funvill/mixxtape/artwork/mixxtape-b-side-peony-flower-centres-template-100-33mm-300dpi.png

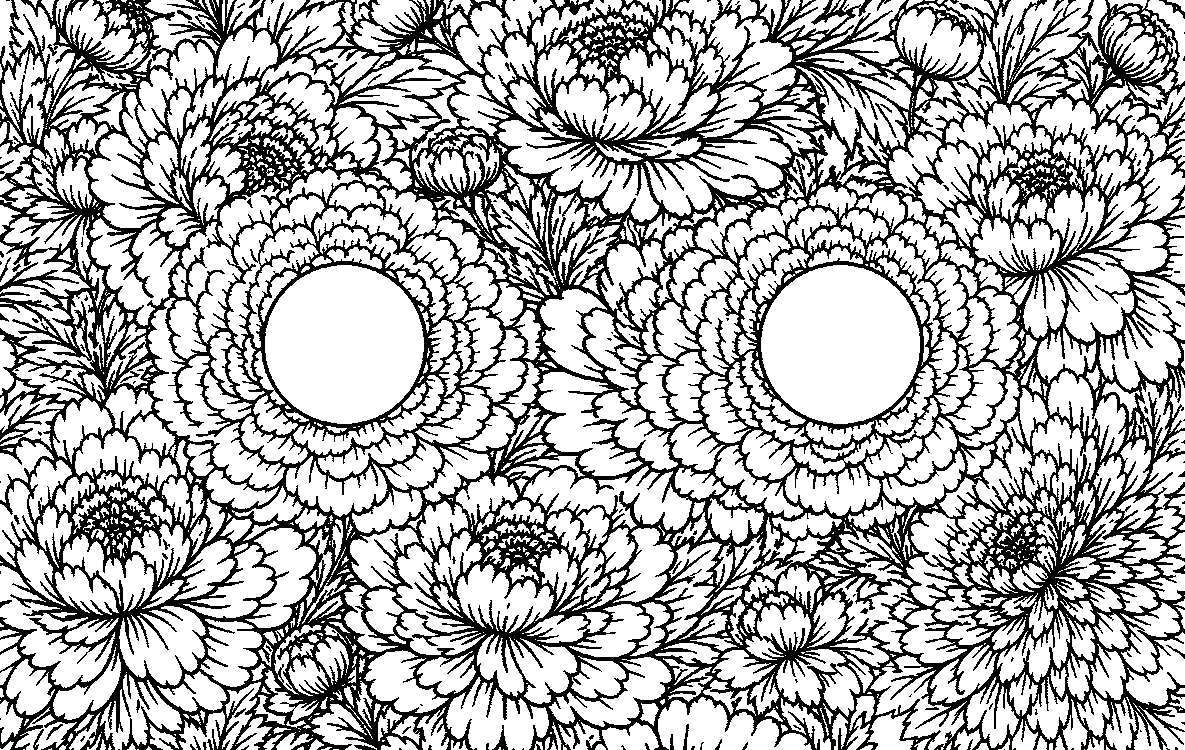
artwork/mixxtape-b-side-peony-flower-centres-template-100-33mm-300dpi.png
