funvill/mixxtape/artwork/robot.png

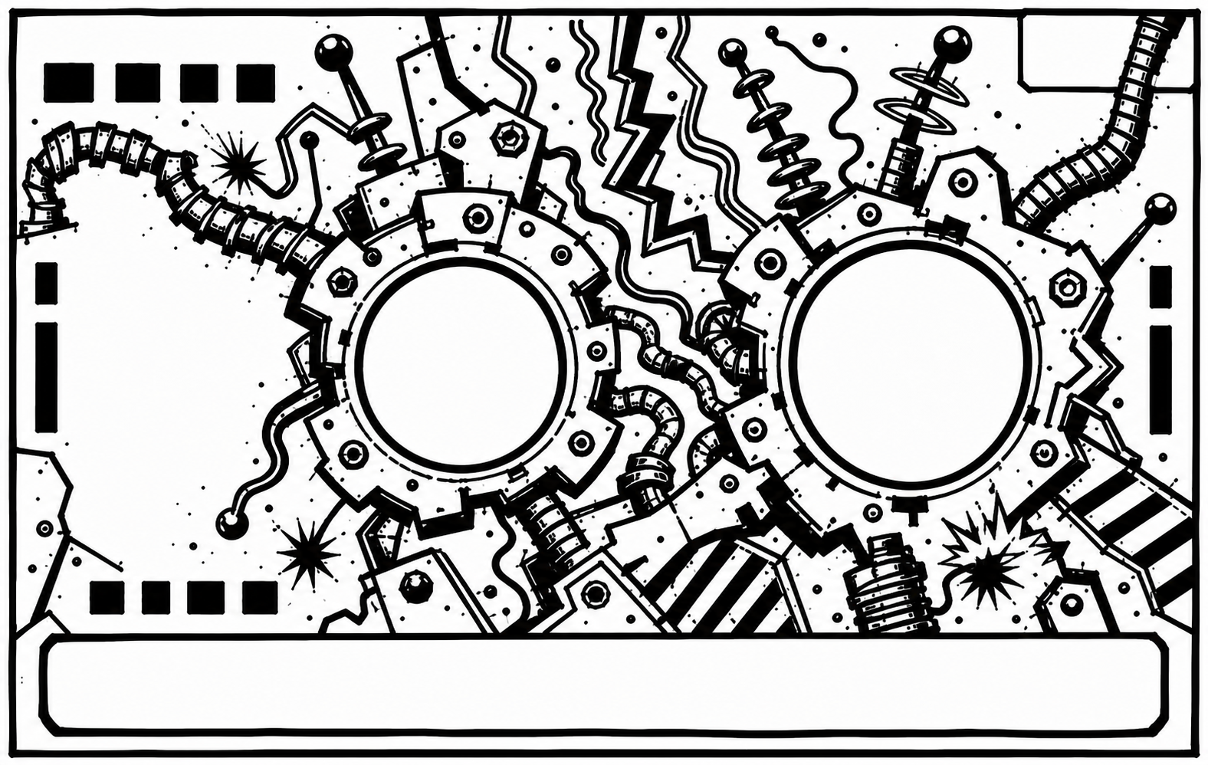
artwork/robot.png
